hallskelet/OctoPrint-Octokeys/BOARD/Schematic/REV_1.sch

## EAGLE design BOARD/Schematic/REV_1.sch (2019-01-21)

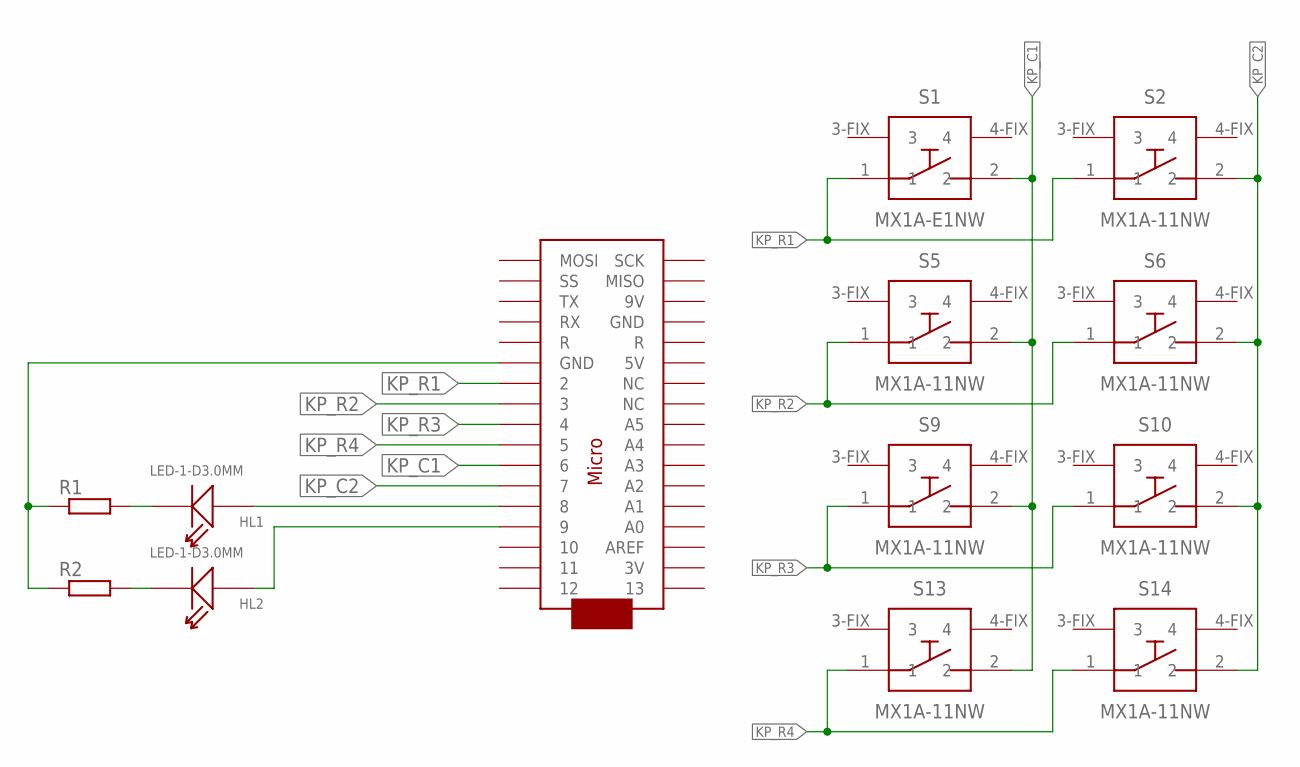
[picture p17: schematic REV_1.sch]

Parts:
HL1, HL2: LED-1-D3.0MM; LED2-2.54-D3.0MM
R1, R2: R-EU_VTA52; VTA52
S1: MX1A-E1NW; MX1A-11NW_1
S2, S5, S6, S9, S10, S13, S14: MX1A-11NW; MX1A-11NW_1
U$2: ARDUINOMICRO

Connections:
KP_C1: S1.2, S5.2, S9.2, S13.2, U$2.P$7 (6)
KP_C2: S2.2, S6.2, S10.2, S14.2, U$2.P$6 (7)
KP_R1: S1.1, S2.1, U$2.P$11 (2)
KP_R2: S5.1, S6.1, U$2.P$10 (3)
KP_R3: S9.1, S10.1, U$2.P$9 (4)
KP_R4: S13.1, S14.1, U$2.P$8 (5)
unnamed: HL1.-, R1.2
unnamed: HL2.+, U$2.P$4 (9)
unnamed: HL2.-, R2.2
unnamed: HL1.+, U$2.P$5 (8)
unnamed: R1.1, R2.1, U$2.P$21 (GND)
